ingegno/fecube/manual/img/n01_rgbledtest_bb.png

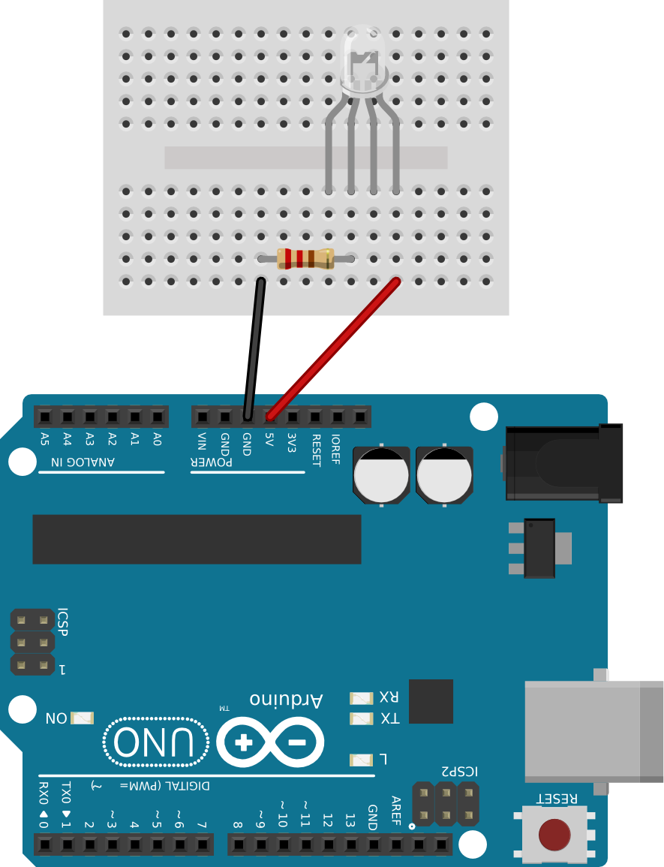
manual/img/n01_rgbledtest_bb.png
