ingegno/fecube/manual/img/n02_rgbledsturing_bb.png

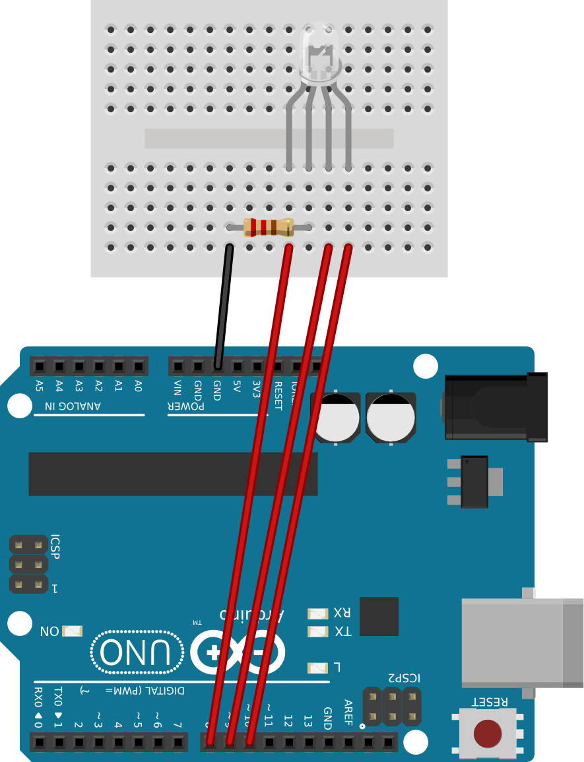
manual/img/n02_rgbledsturing_bb.png
