ingegno/fecube/manual/img/n03_rgblednpn_bb.png

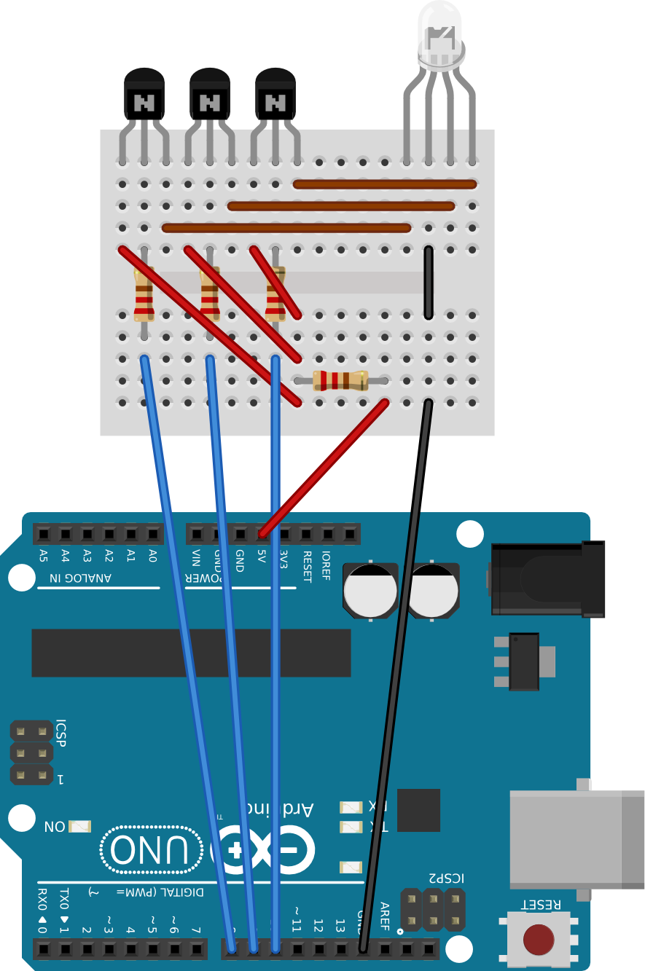
manual/img/n03_rgblednpn_bb.png
