ingegno/fecube/manual/img/n04_rgbledmultiplex_bb.png

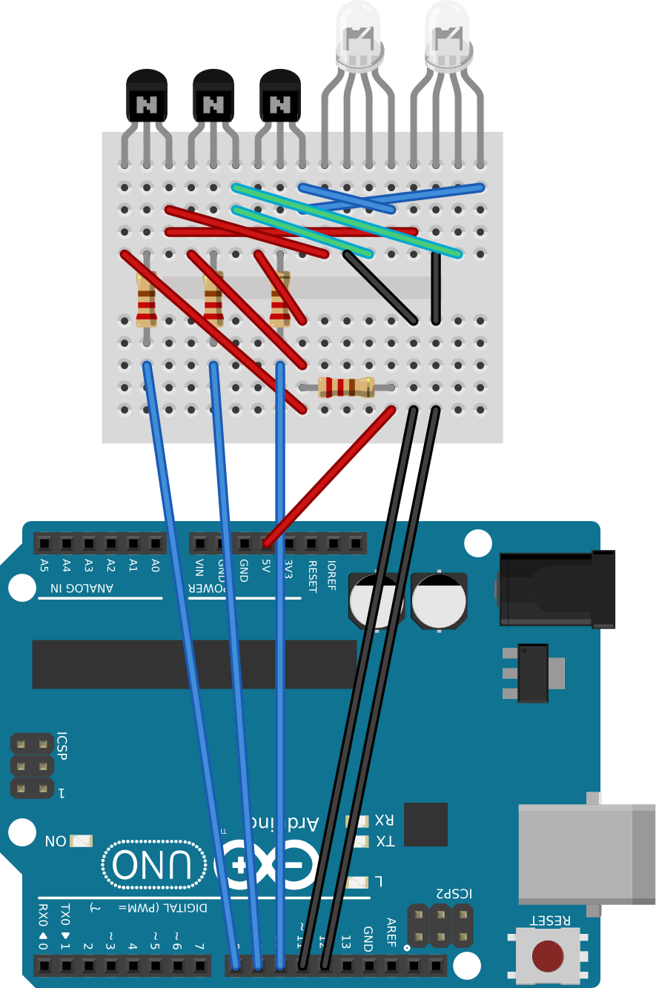
manual/img/n04_rgbledmultiplex_bb.png
