ingegno/fecube/manual/img/n05_fecube_bb.png

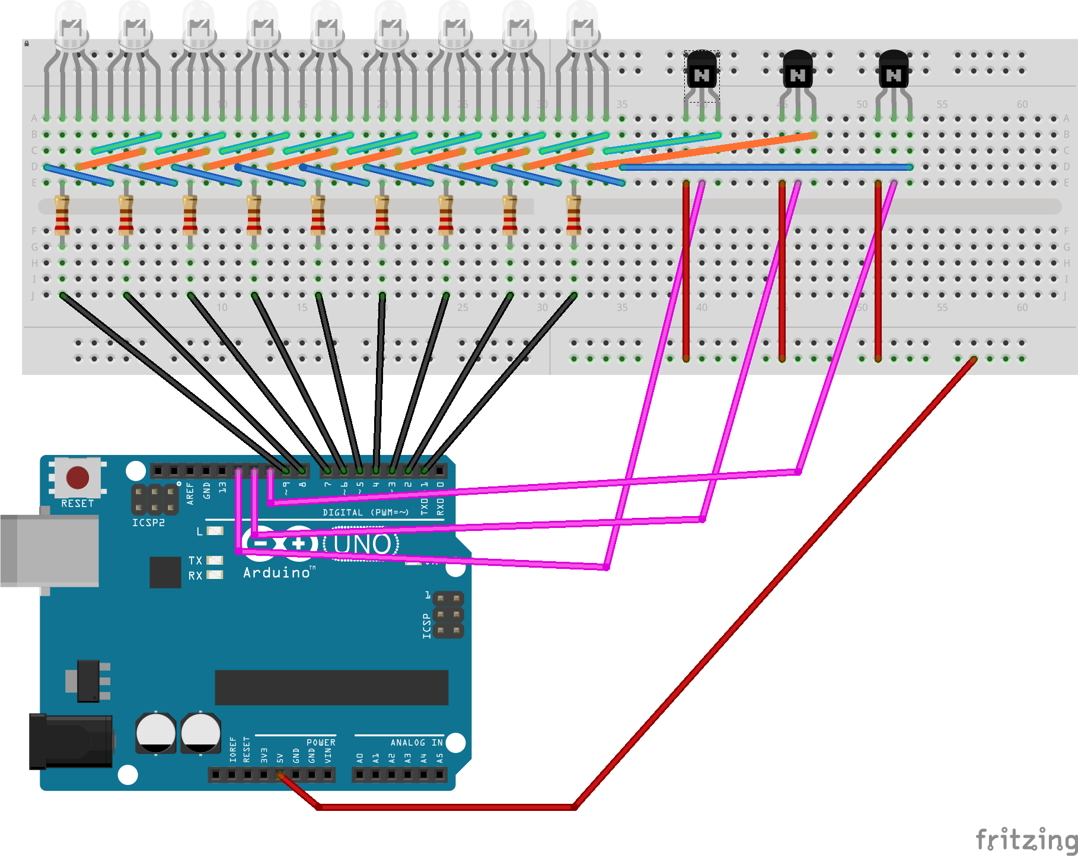
manual/img/n05_fecube_bb.png
