ingegno/fecube/manual/img/n07_pushbutton_status_bb.png

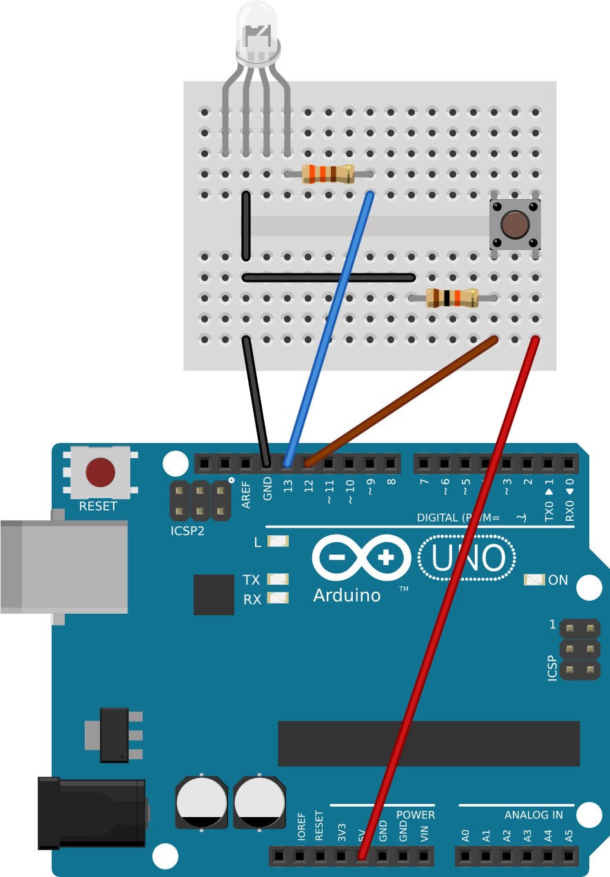
manual/img/n07_pushbutton_status_bb.png
