ingegno/fecube/manual/pic/constr_01.JPG

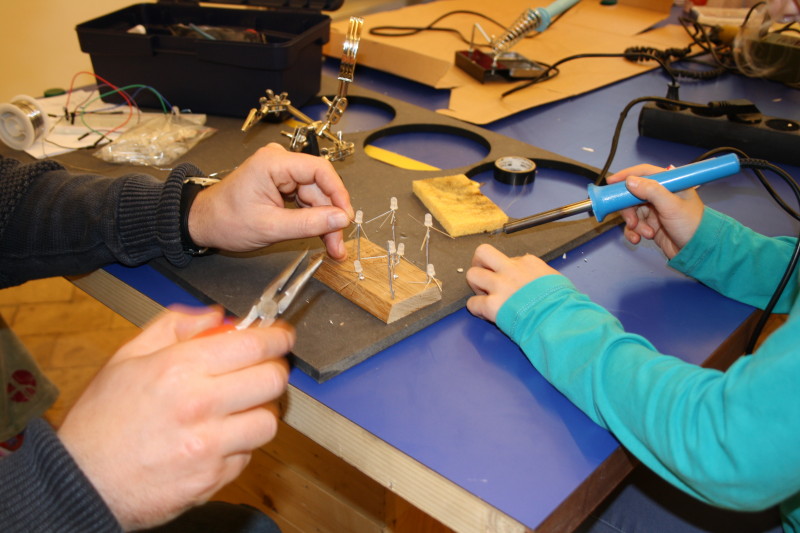
manual/pic/constr_01.JPG
