ingegno/fecube/manual/pic/constr_02.JPG

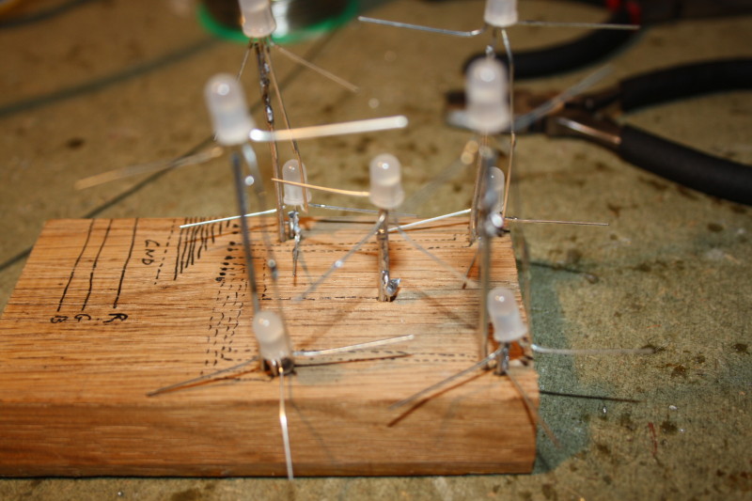
manual/pic/constr_02.JPG
