ingegno/fecube/manual/pic/constr_03.JPG

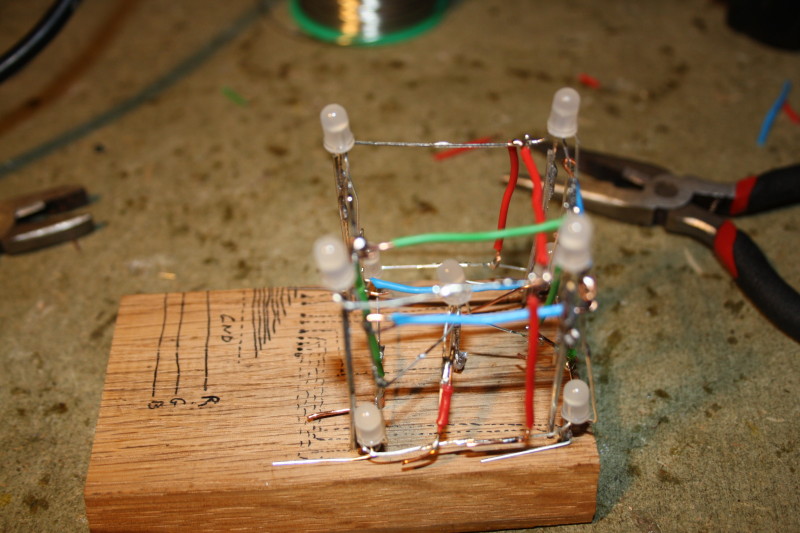
manual/pic/constr_03.JPG
