ingegno/fecube/manual/pic/prototype01.JPG

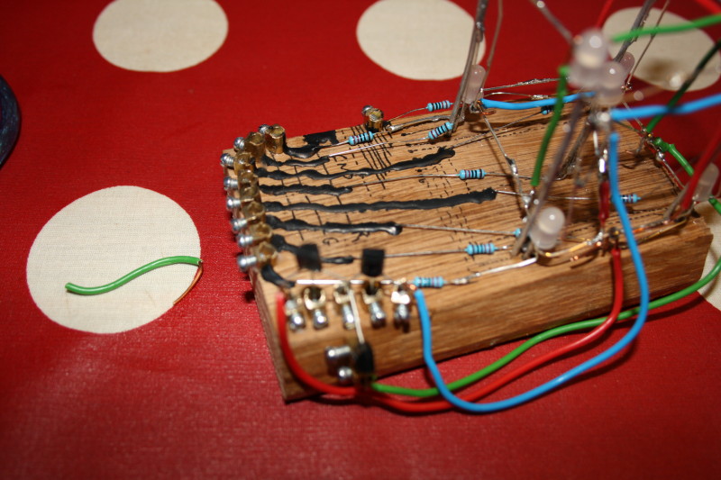
manual/pic/prototype01.JPG
