ingegno/fecube/manual/pic/prototype02_a.JPG

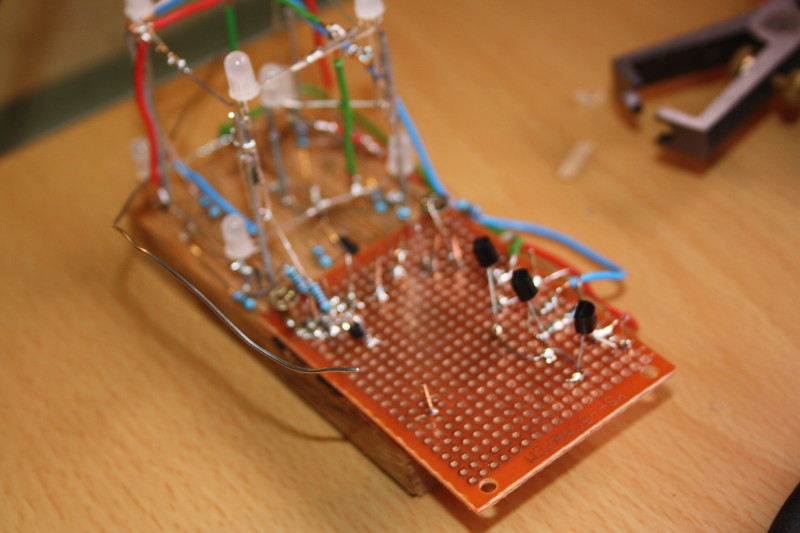
manual/pic/prototype02_a.JPG
