ingegno/fecube/manual/pic/prototype02_b.JPG

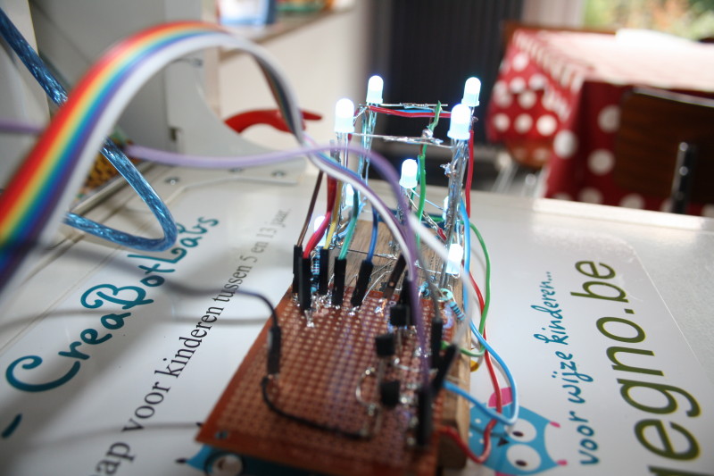
manual/pic/prototype02_b.JPG
