ingegno/fecube/manual/pic/prototype03_c.JPG

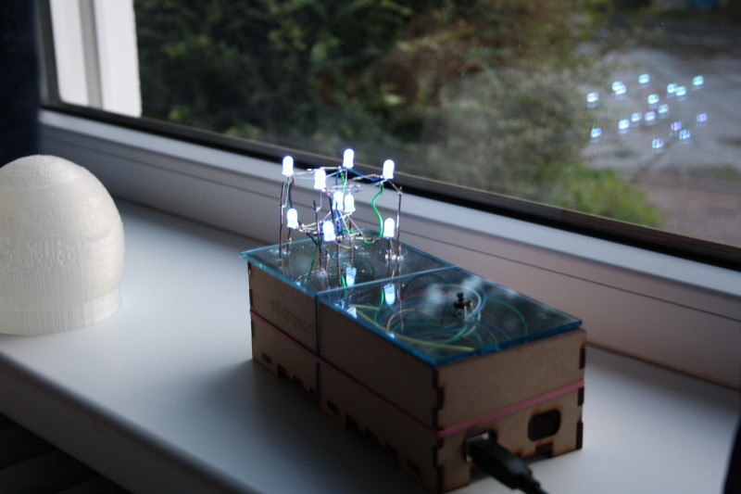
manual/pic/prototype03_c.JPG
