ingegno/fecube/manual/png/ardschemnpn.JPG

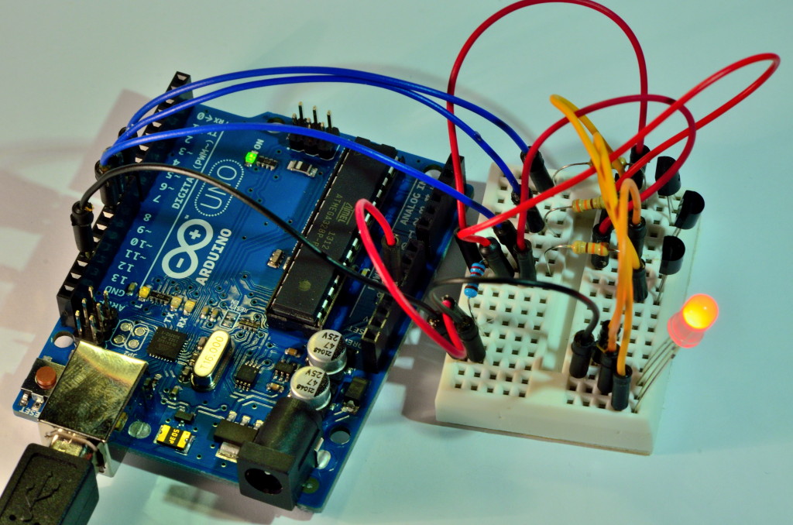
manual/png/ardschemnpn.JPG
