ingegno/fecube/manual/png/atomium.jpg

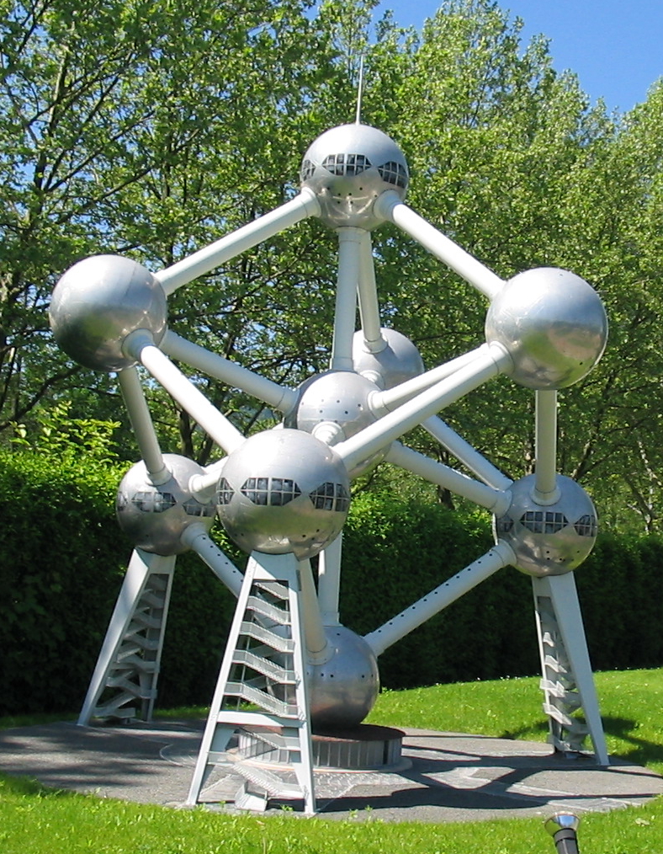
manual/png/atomium.jpg
