ingegno/fecube/manual/png/constructie_02.JPG

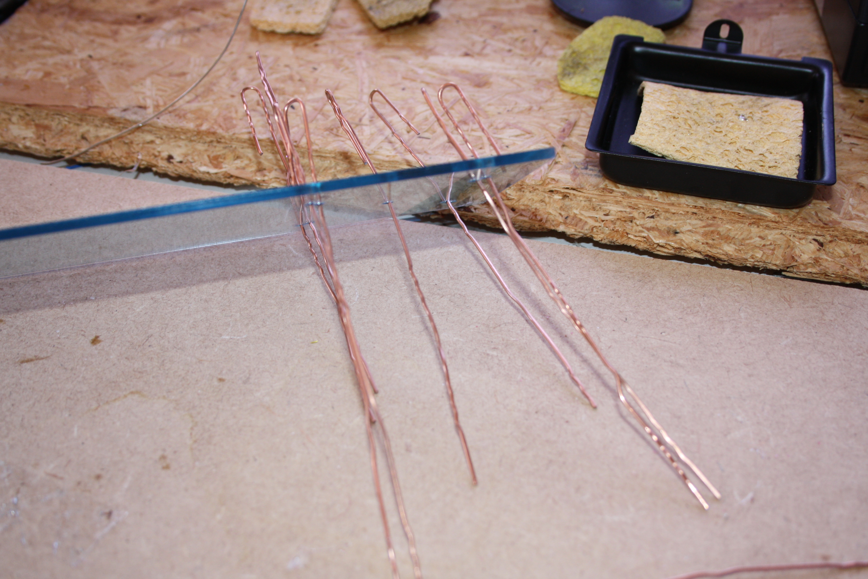
manual/png/constructie_02.JPG
