ingegno/fecube/manual/png/constructie_03.JPG

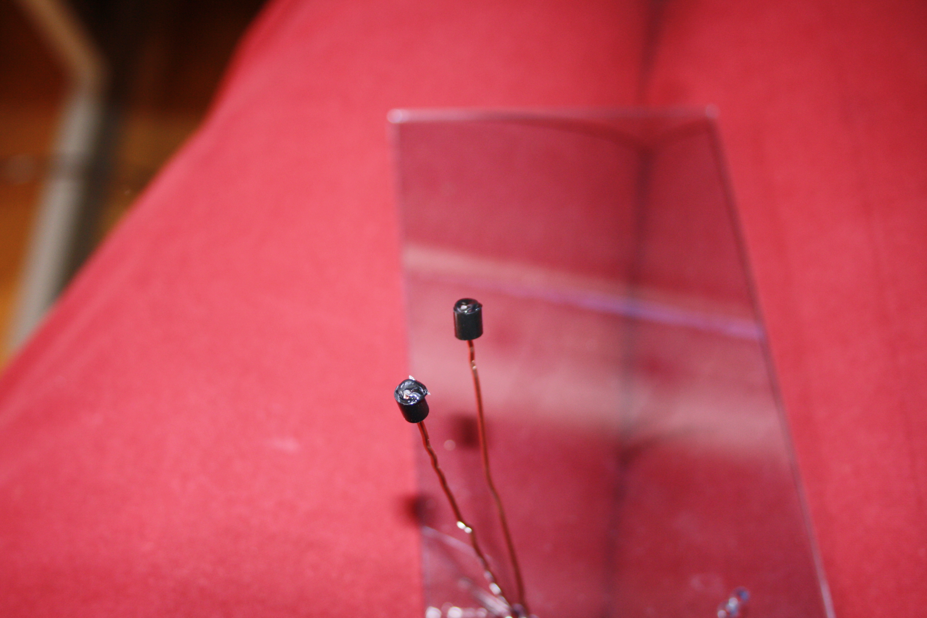
manual/png/constructie_03.JPG
