ingegno/fecube/manual/png/constructie_04.JPG

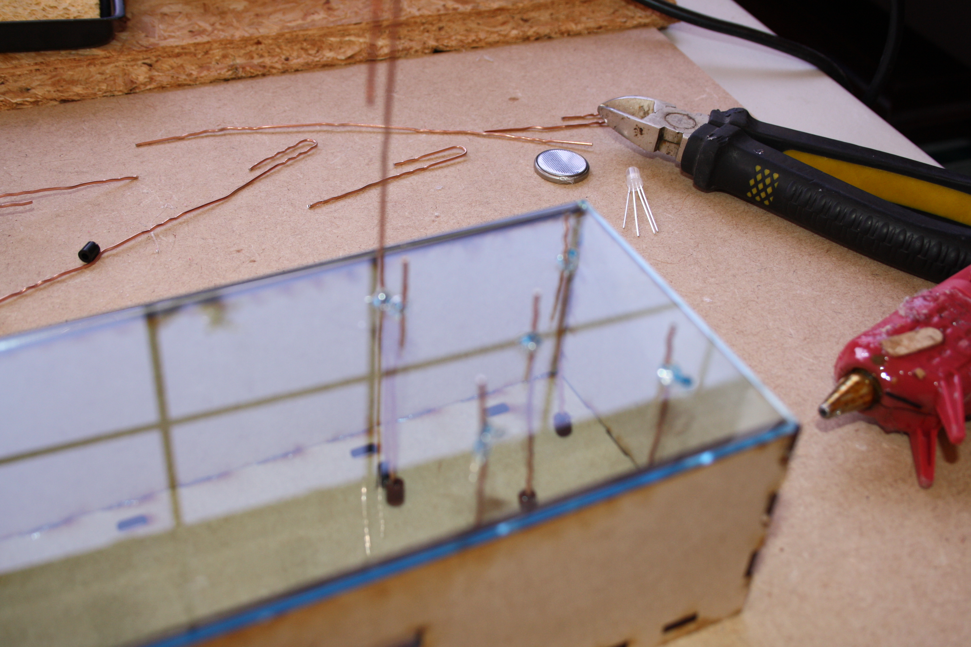
manual/png/constructie_04.JPG
