ingegno/fecube/manual/png/constructie_05.JPG

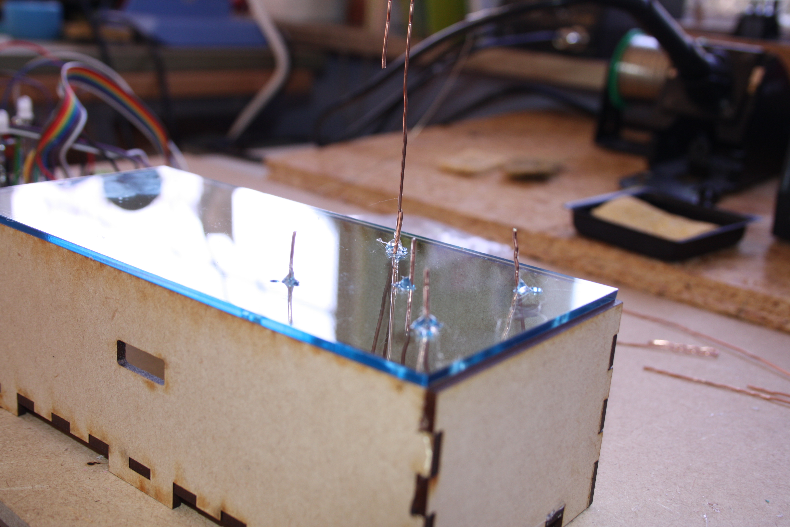
manual/png/constructie_05.JPG
