ingegno/fecube/manual/png/constructie_06.JPG

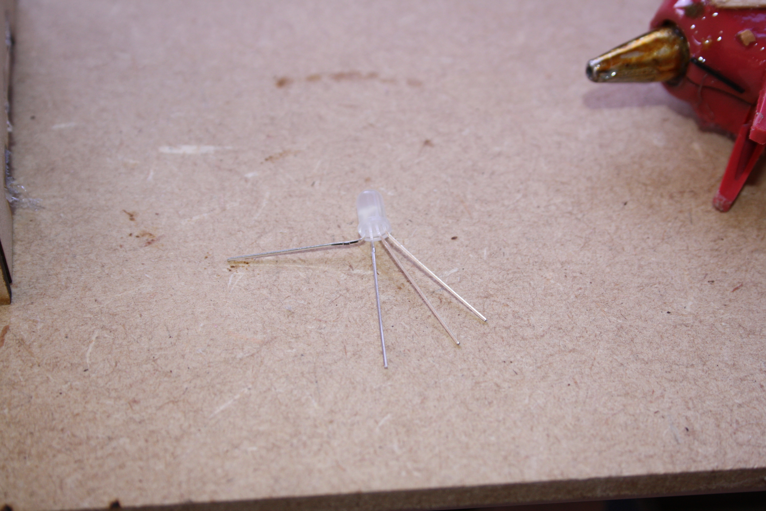
manual/png/constructie_06.JPG
