ingegno/fecube/manual/png/constructie_07.JPG

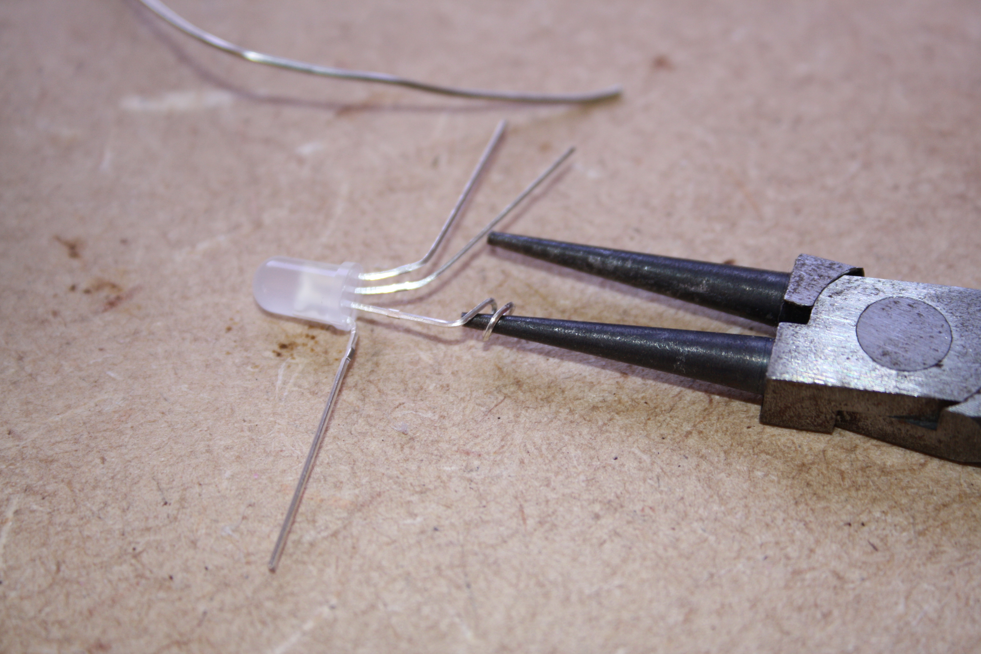
manual/png/constructie_07.JPG
