ingegno/fecube/manual/png/constructie_08.JPG

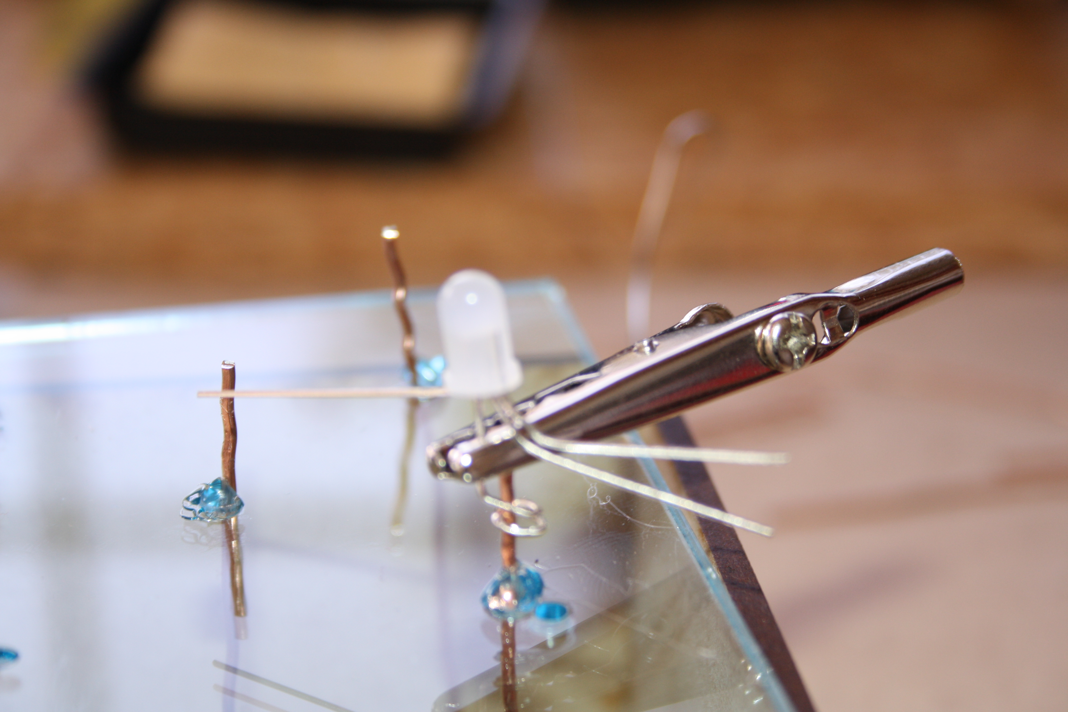
manual/png/constructie_08.JPG
