ingegno/fecube/manual/png/constructie_09.JPG

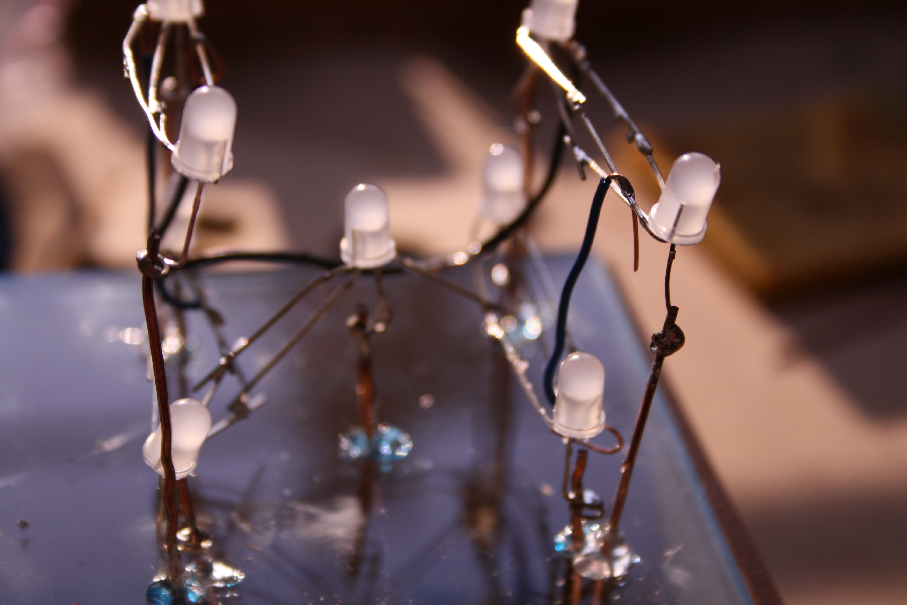
manual/png/constructie_09.JPG
