ingegno/fecube/manual/png/constructie_10.JPG

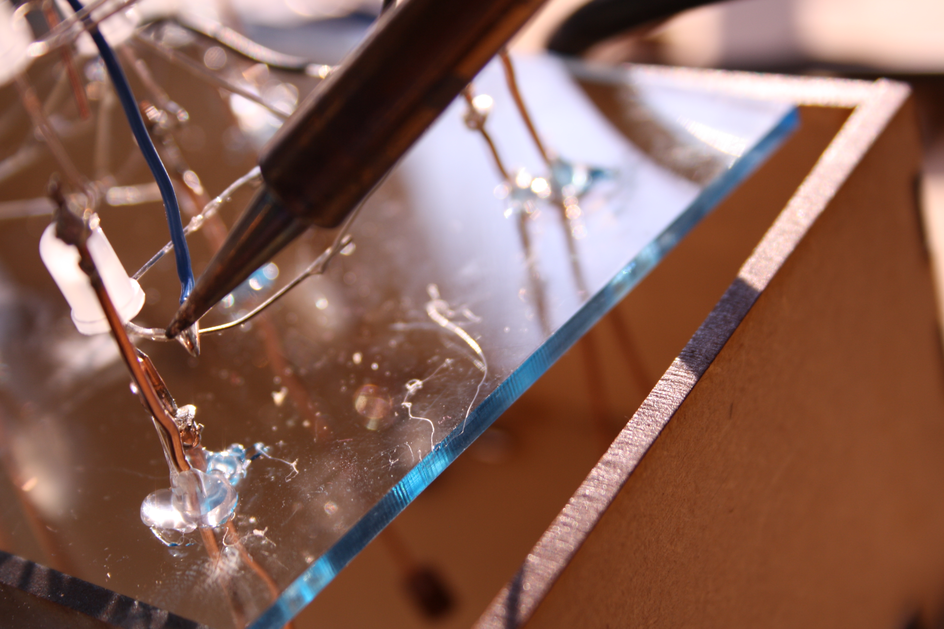
manual/png/constructie_10.JPG
