ingegno/fecube/manual/png/constructie_11.JPG

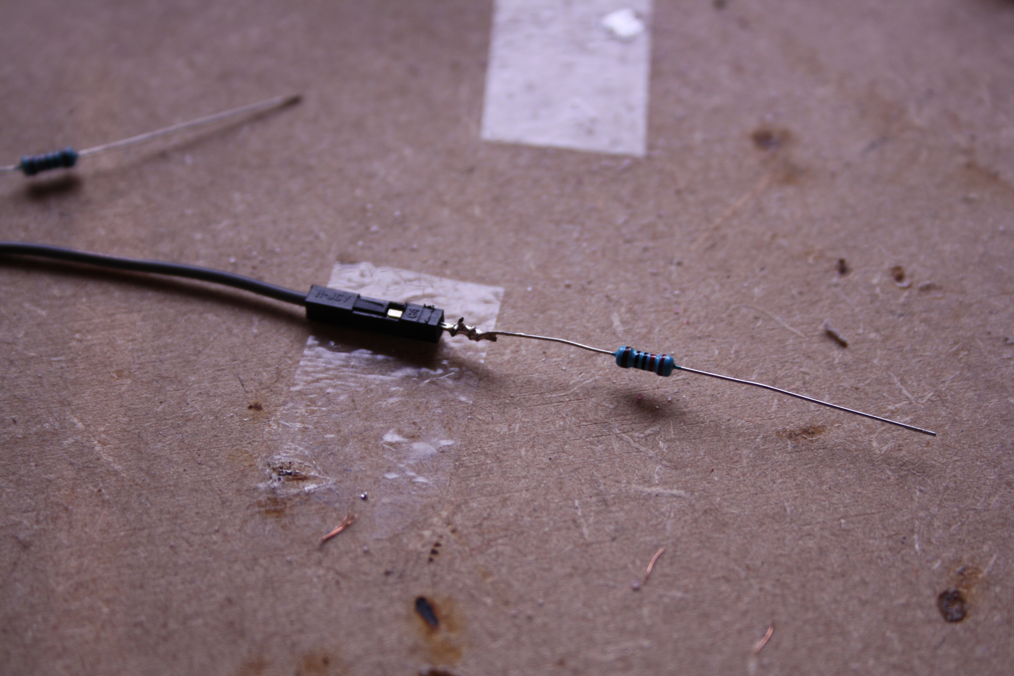
manual/png/constructie_11.JPG
