ingegno/fecube/manual/png/constructie_12.JPG

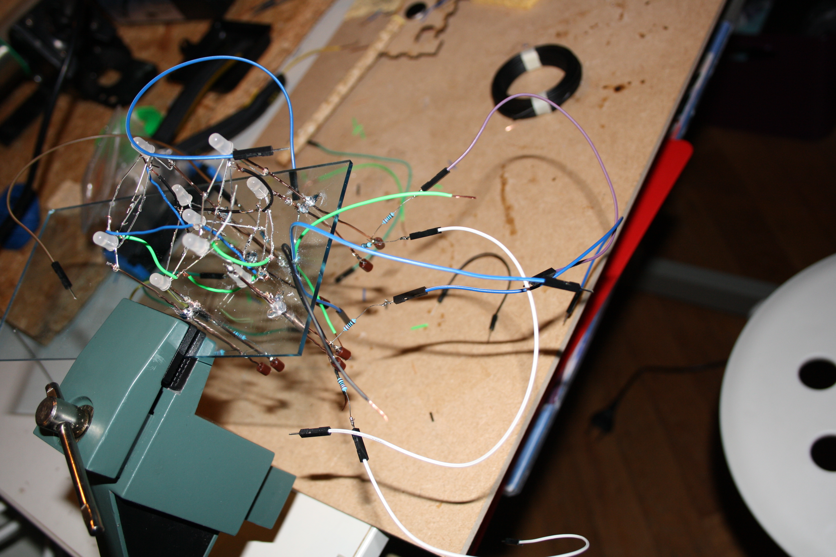
manual/png/constructie_12.JPG
