ingegno/fecube/manual/png/constructie_13.JPG

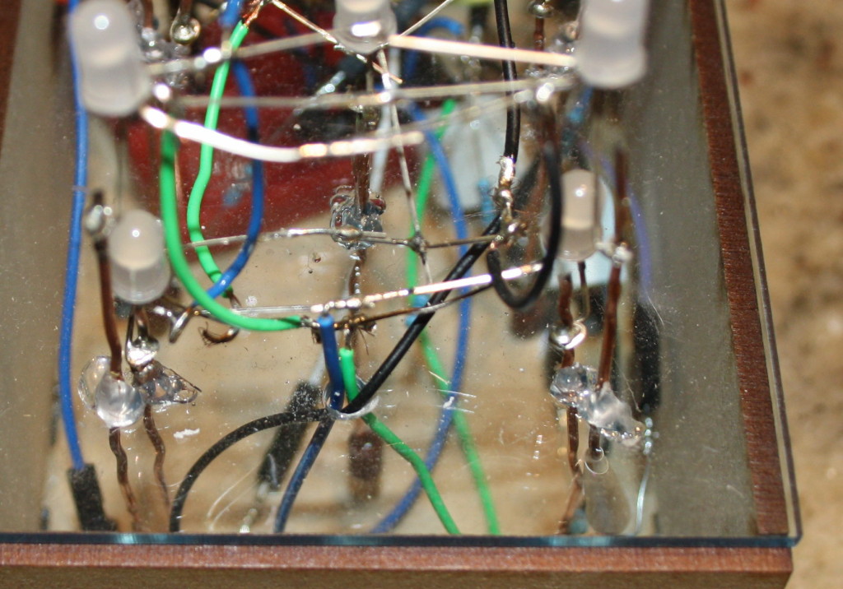
manual/png/constructie_13.JPG
