ingegno/fecube/manual/png/constructie_14.JPG

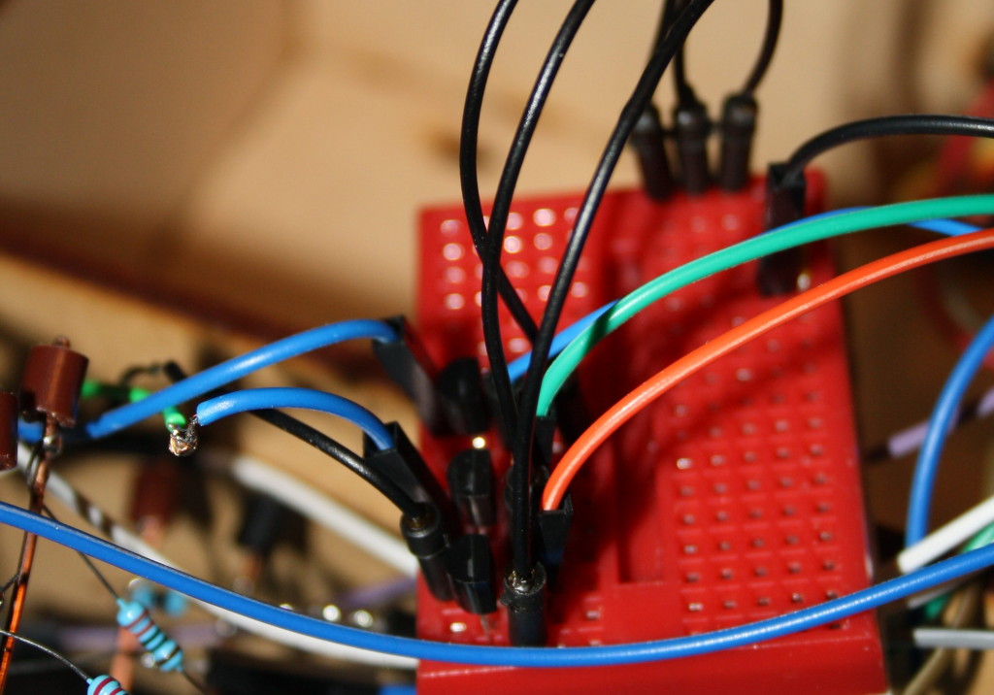
manual/png/constructie_14.JPG
