ingegno/fecube/manual/png/constructie_15.JPG

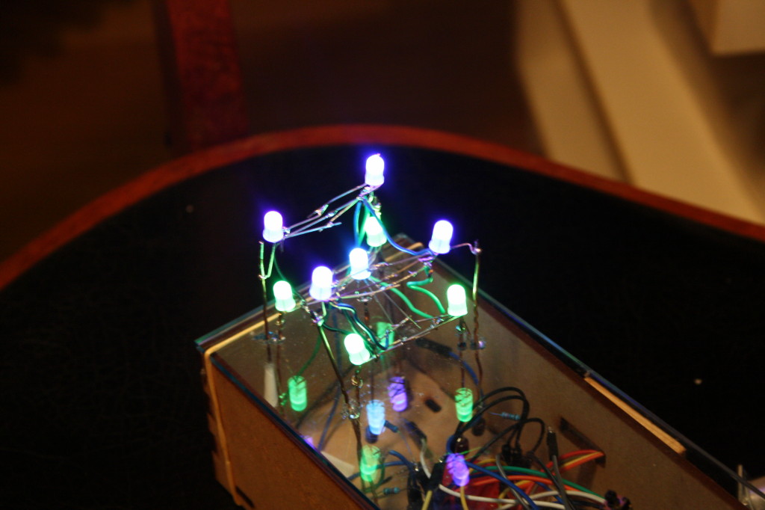
manual/png/constructie_15.JPG
