ingegno/fecube/manual/png/constructie_16.JPG

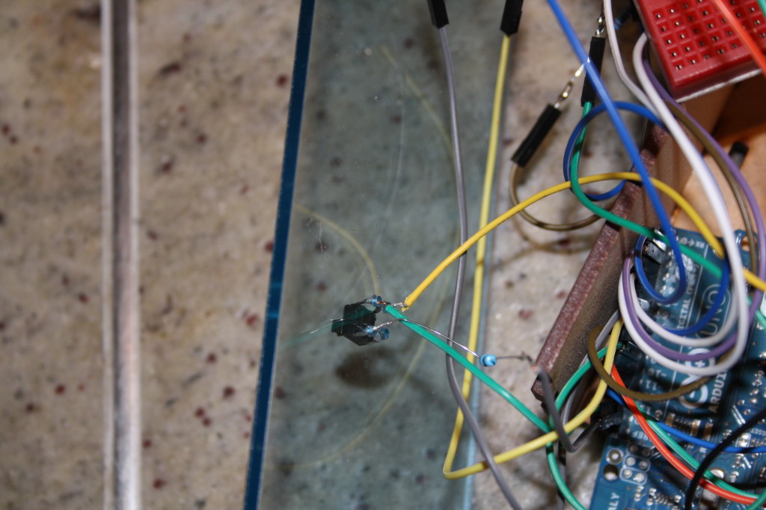
manual/png/constructie_16.JPG
