ingegno/fecube/manual/png/constructie_01.JPG

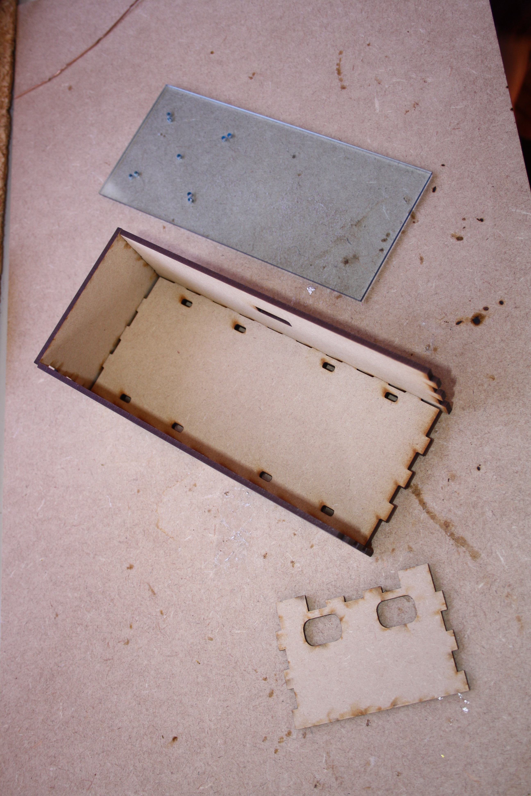
manual/png/constructie_01.JPG
